sergio-alves/NitroxAnalyzer/docs/images/20160120_213357.jpg

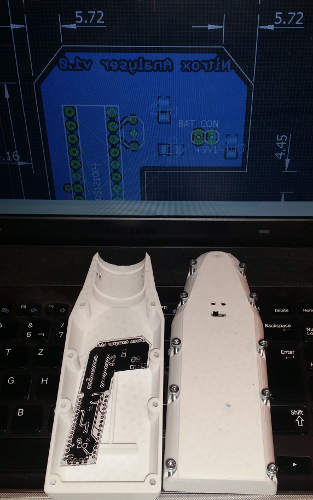
docs/images/20160120_213357.jpg
