sergio-alves/NitroxAnalyzer/docs/images/20160121_104506.jpg

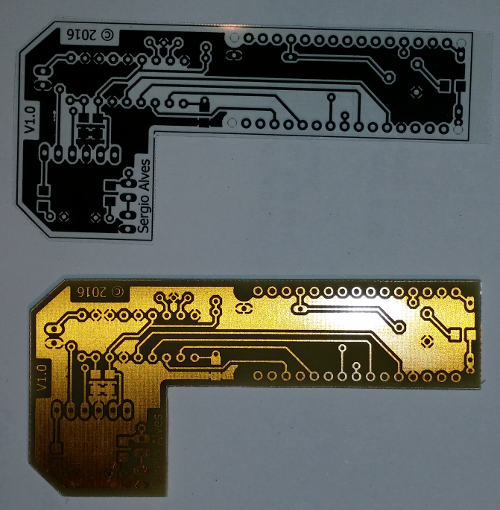
docs/images/20160121_104506.jpg
