sergio-alves/NitroxAnalyzer/docs/images/20160121_110440.jpg

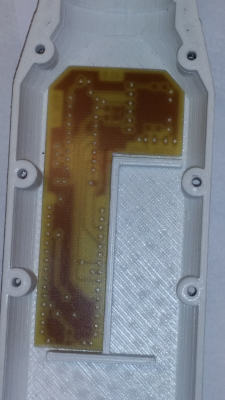
docs/images/20160121_110440.jpg
