sergio-alves/NitroxAnalyzer/docs/images/20160121_203556.jpg

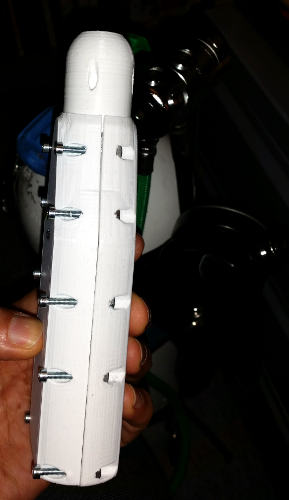
docs/images/20160121_203556.jpg
